Arroyador69/nfctap.tech/media/assets/bank/proceso/README.txt

CUERPO · PROCESO de impresión.

Carpeta:
  /Users/albertogarciaarroyo/impresora 3d/media/assets/bank/proceso/

Pega aquí MOV/MP4 del hacer: FlashPrint, capa a capa, pausa NFC, insertar
chip, pieza saliendo, pintar, montar cuna…

Cualquier vídeo vale. Si el título lleva tap / generica / dos / personalizada
el pack lo empareja al tema del Reel.

Un MOV nuevo aquí entra en el siguiente pack (no reutiliza los ya publicados).
