Arroyador69/nfctap.tech/media/assets/bank/web/README.txt

CIERRE · grabación LARGA de nfctap.tech en uso.

Carpeta:
  /Users/albertogarciaarroyo/impresora 3d/media/assets/bank/web/

Pega aquí el MOV/MP4 nuevo (puede durar lo que quiera). Si dejas el viejo,
el pack usa el más pesado (el largo).

Cada Reel corta un trozo distinto (~6 s) y va recorriendo el vídeo.
Entre todos los Reels se ve casi entero. No recorta siempre el mismo segundo 8.
