Arroyador69/nfctap.tech/media/assets/bank/imagenes/README.txt

Pega al menos 3 fotos JPG, PNG, WEBP o HEIC del atril.

Si pones solo 3, salen en orden de nombre (01.jpg, 02.jpg, 03.jpg).
El iPhone en HEIC vale: el sistema lo pasa a JPG.
