Arroyador69/nfctap.tech/comercial/web/NFCTap-presupuesto-web.jpg

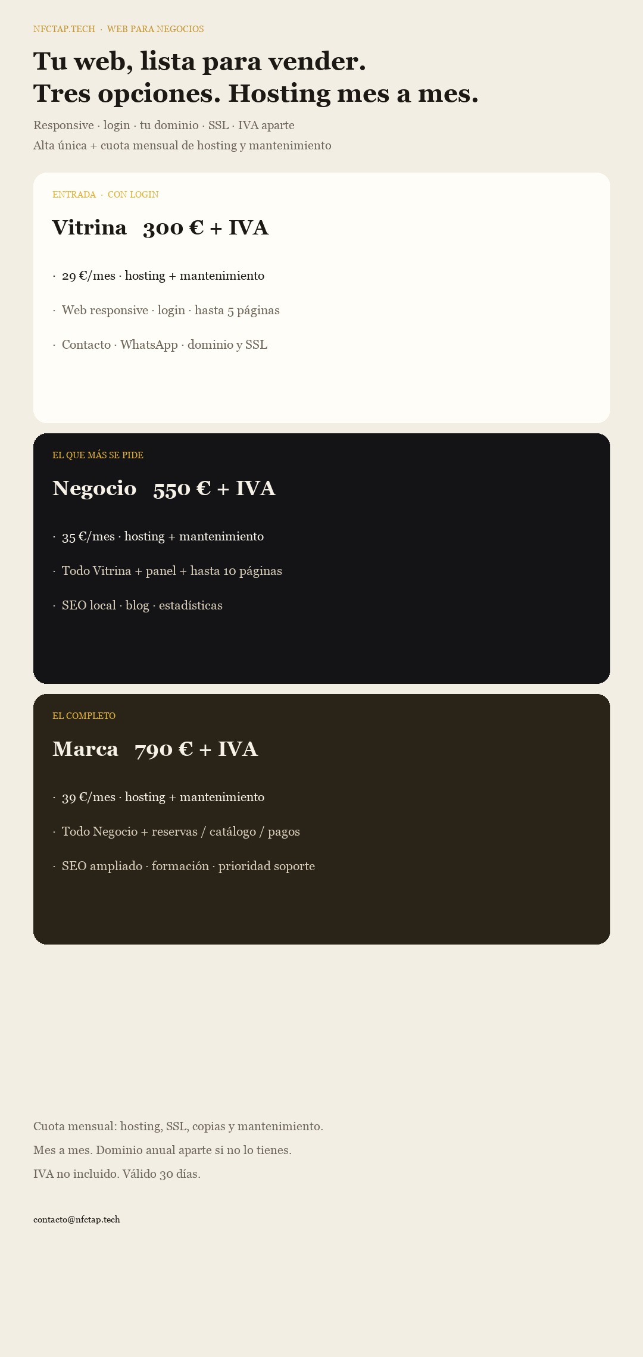
comercial/web/NFCTap-presupuesto-web.jpg
