Arroyador69/nfctap.tech/disenos/stl/generica-blanca-negra/propuesta.jpg

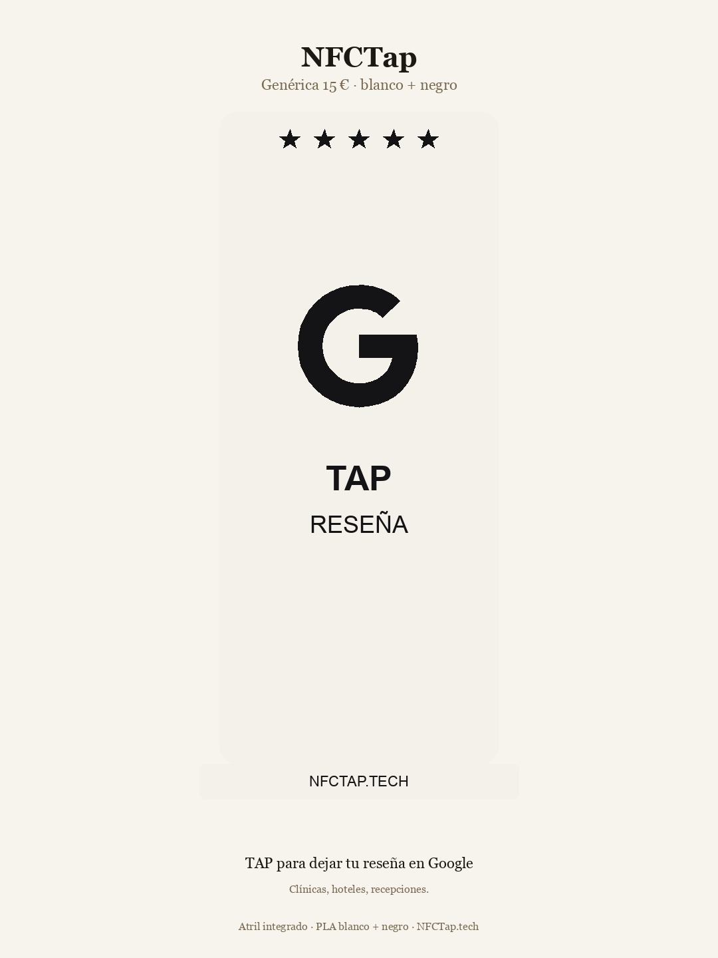
disenos/stl/generica-blanca-negra/propuesta.jpg
