Arroyador69/nfctap.tech/disenos/stl/boton-nfctap/03_aro.stl

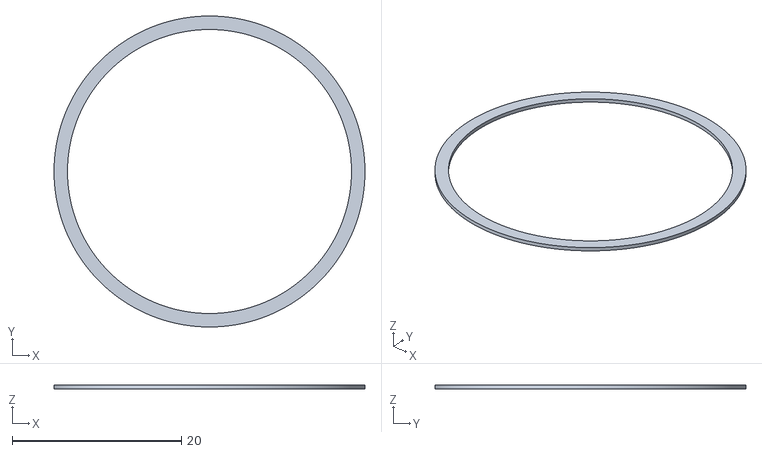
[picture p22: CAD file, 2026-09-27]
disenos/stl/boton-nfctap/03_aro.stl
36.8 x 36.8 x 0.45
