Arroyador69/nfctap.tech/disenos/stl/freddos-fuengirola/fredos grano.3mf

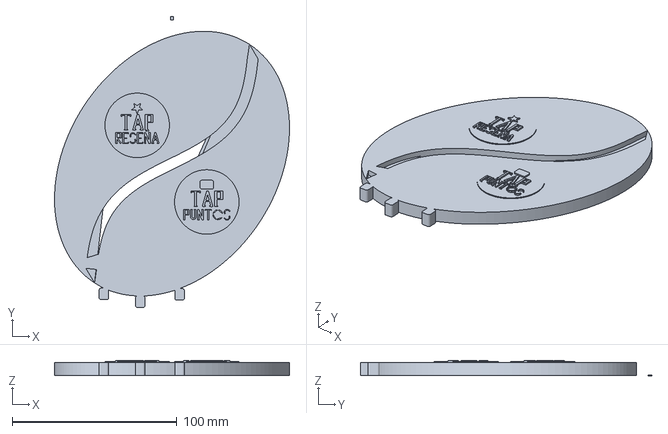
[picture p23: CAD file, 2026-09-10]
disenos/stl/freddos-fuengirola/fredos grano.3mf
142.8 x 176.8 x 9.40 mm
