Arroyador69/nfctap.tech/disenos/stl/boton-nfctap/01_cuerpo.stl

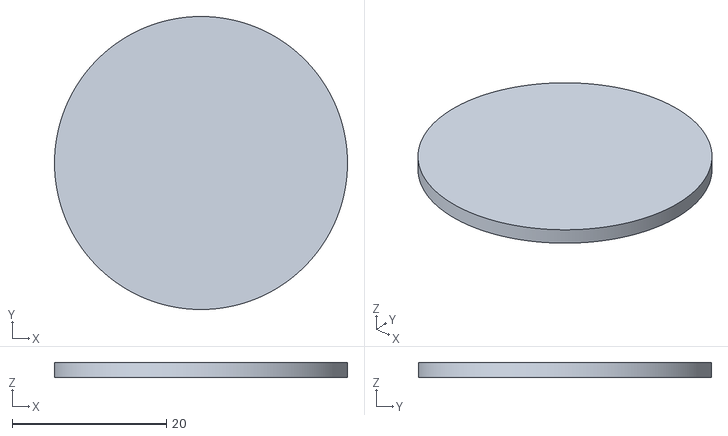
[picture p24: CAD file, 2026-09-27]
disenos/stl/boton-nfctap/01_cuerpo.stl
38.0 x 38.0 x 2.00
