Arroyador69/nfctap.tech/disenos/stl/freddos-fuengirola/01_grano_negro.stl

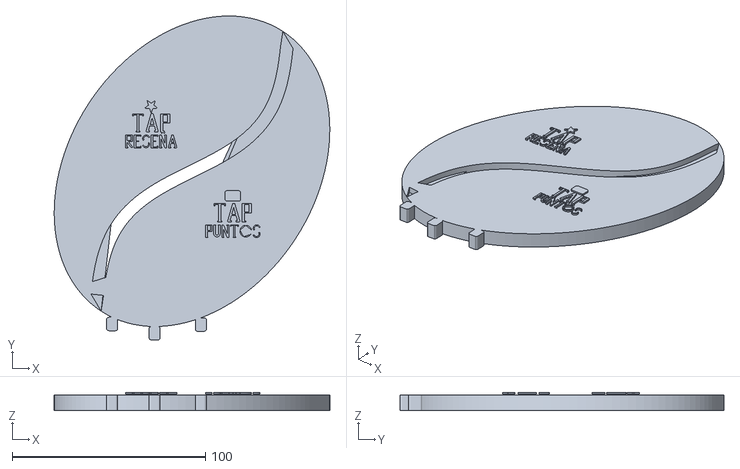
[picture p25: CAD file, 2026-09-10]
disenos/stl/freddos-fuengirola/01_grano_negro.stl
142.8 x 167.8 x 9.40
