Arroyador69/nfctap.tech/disenos/stl/freddos-fuengirola/02_grano_oro.stl

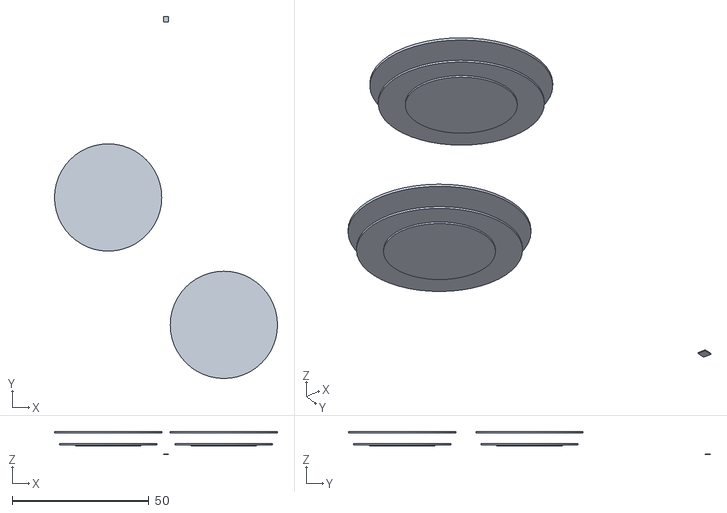
[picture p26: CAD file, 2026-09-10]
disenos/stl/freddos-fuengirola/02_grano_oro.stl
81.5 x 132.3 x 8.55
