Arroyador69/nfctap.tech/disenos/stl/generica-blanca-negra/01_cuerpo.stl

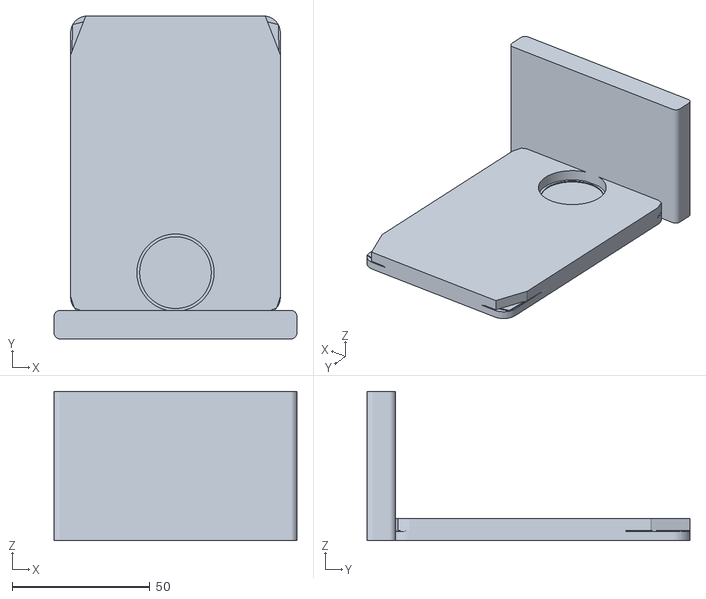
[picture p27: CAD file, 2026-09-08]
disenos/stl/generica-blanca-negra/01_cuerpo.stl
88.0 x 117.0 x 54.0
